MitchellStride/Clock-Module/images/20251205_routed.png

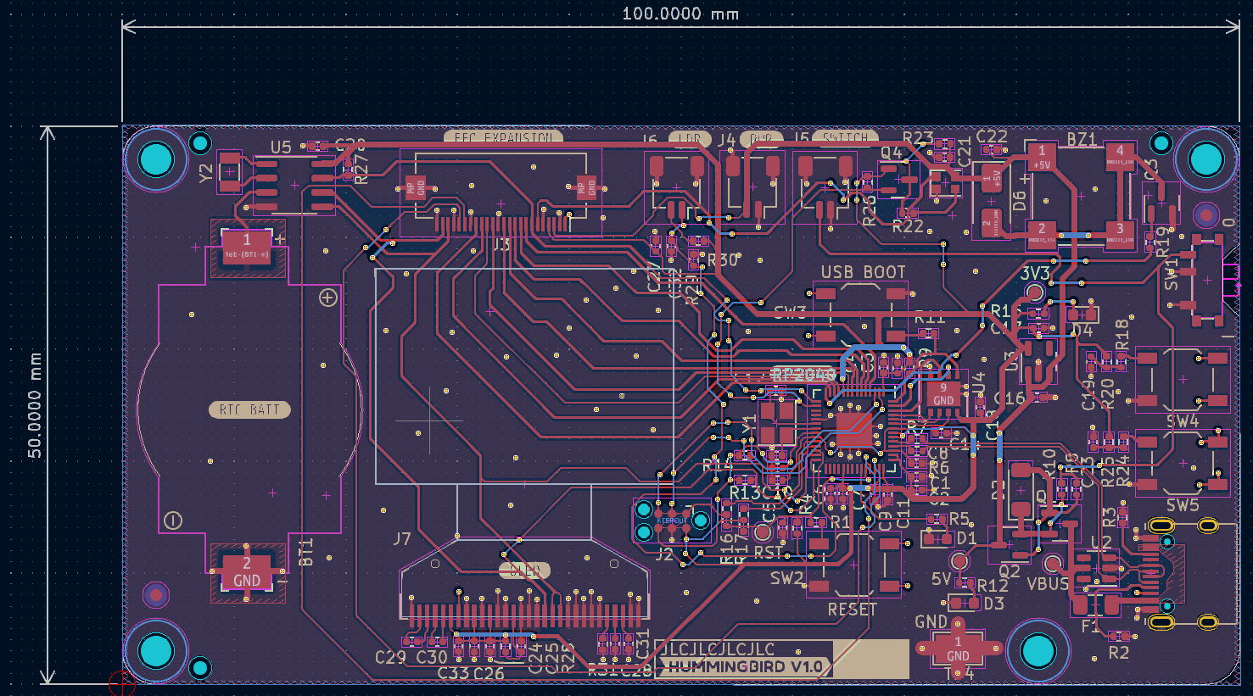
images/20251205_routed.png
