MitchellStride/Clock-Module/images/20251205_top3d.png

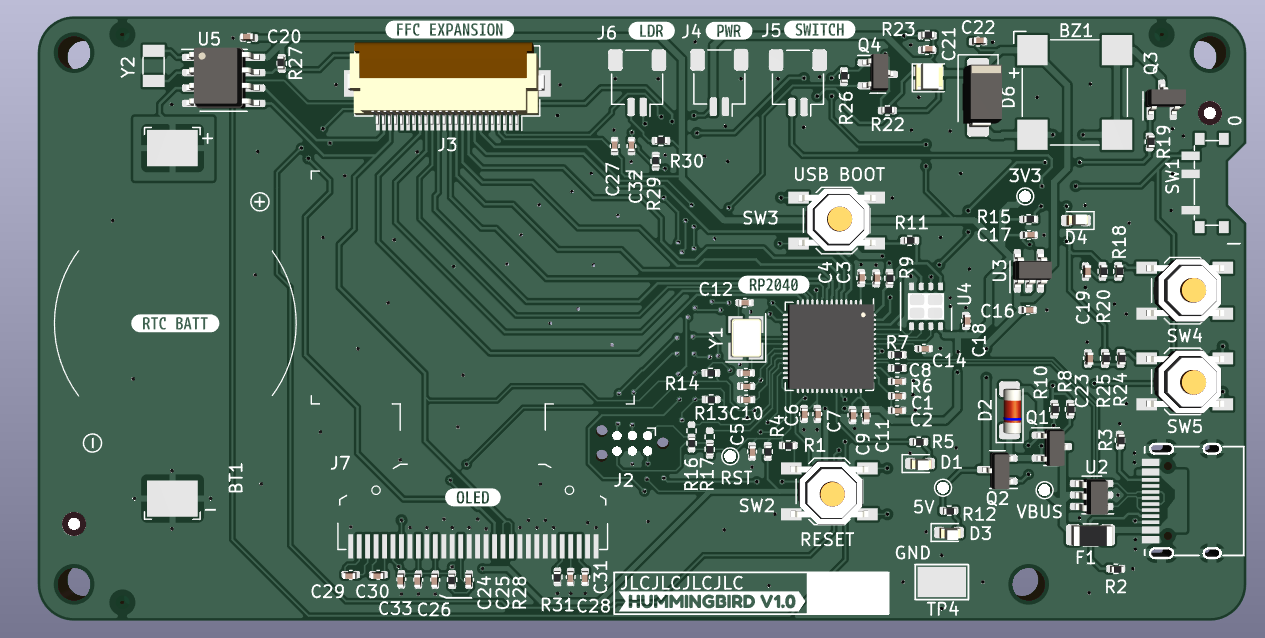
images/20251205_top3d.png
