MitchellStride/Clock-Module/images/assets/flower.PNG

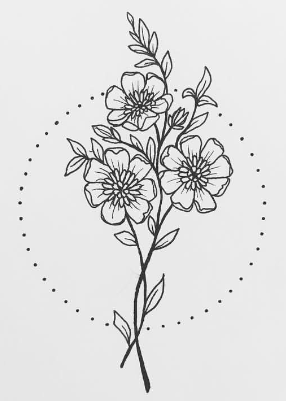
images/assets/flower.PNG
