MitchellStride/Clock-Module/images/assets/hummingbird.PNG

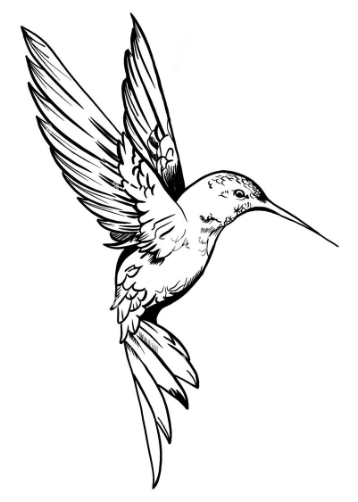
images/assets/hummingbird.PNG
