MitchellStride/Clock-Module/images/cost2.png

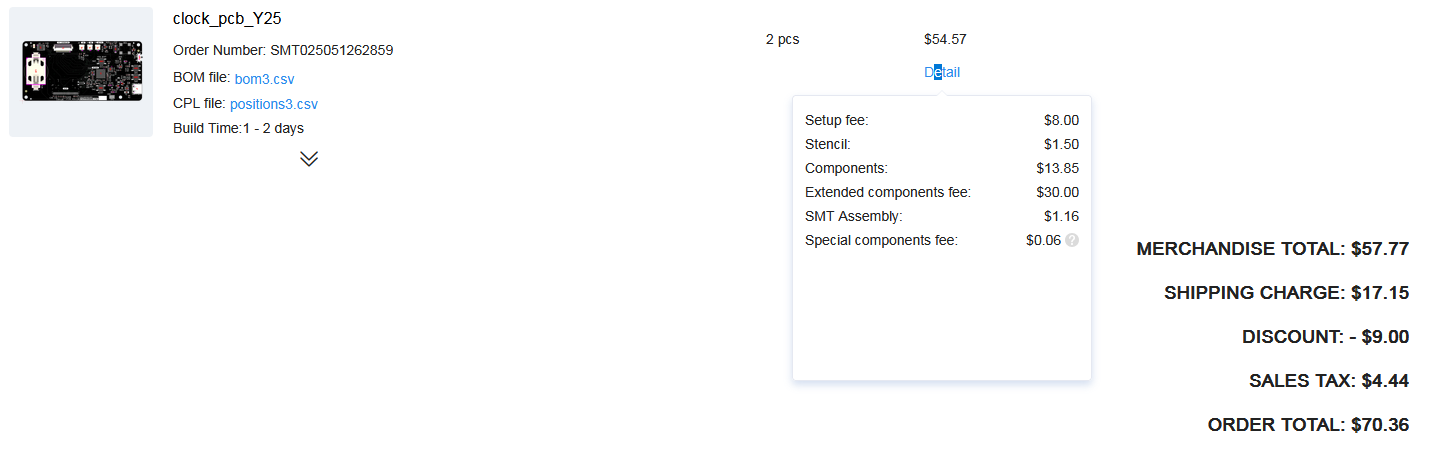
images/cost2.png
