MitchellStride/Clock-Module/images/cost.png

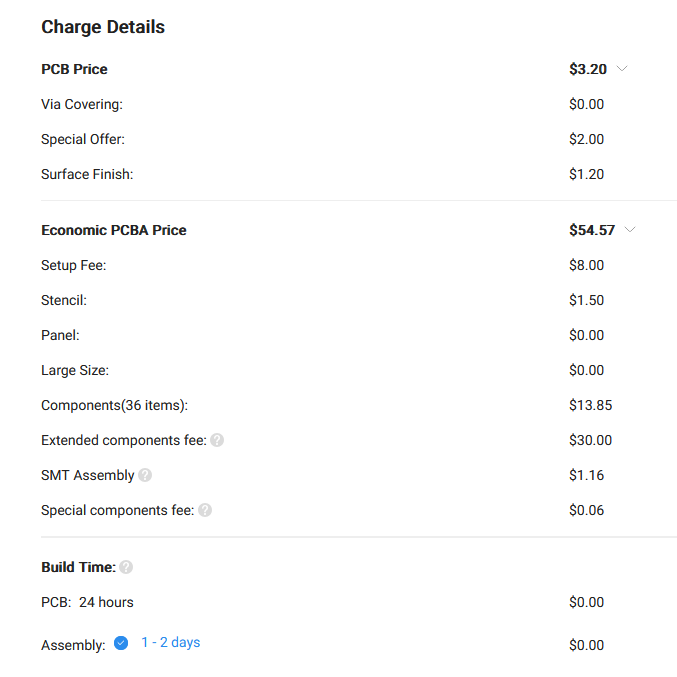
images/cost.png
