MitchellStride/Clock-Module/simulation/buzzer2.asc

C1: cap; 10µ
L1: ind; 3m
M1: nmos; ""
R3: res; 0
R5: res; 33
R6: res; 500
V1: voltage; 3.3
V2: voltage; 5
V3: voltage; PULSE(0 3.3 0.25m 0 0 0.25m 0.50m 10)
Named nets: 3V3, 0, 5V, 3v3_PULSE
.include C:\\Users\\stride\\Documents\\GitHub\\Clock-Module\\clock_pcb\\sim\\AO3401.mod
.tran 0.00375
.include C:\\Users\\stride\\Documents\\GitHub\\Clock-Module\\clock_pcb\\sim\\AO3400.mod
.model switch1 SW(Ron=0.2 Roff=10Meg Vt=.5 Vh=-.4)
