MitchellStride/Clock-Module/simulation/buzzer.asc

C1: cap; 10µ
M1: nmos; ""
R3: res; 120
R5: res; 10
R6: res; 10k
V1: voltage; 3.3
V2: voltage; 5
V3: voltage; PULSE(0 5 200m 0 0 200m 400m)
Named nets: 3V3, 0, 5V, 5V_PULSE
.include C:\\projects\\Death-Clock\\clock_pcb\\sim\\AO3401.mod
.tran 1
.include C:\\projects\\Death-Clock\\clock_pcb\\sim\\AO3400.mod
.model switch1 SW(Ron=0.2 Roff=10Meg Vt=.5 Vh=-.4)
