MitchellStride/Clock-Module/simulation/LDR.asc

C1: cap; 0.1µ
R1: res; 10k
R2: res; 10k
R3: res; 1k
V1: voltage; PULSE(0 3.3 0.1m 0.3m 0 1 2 1)
V2: voltage; 5
Named nets: 3V3, 0, 5V, ADC
.tran 50m
LDR
