MitchellStride/Clock-Module/simulation/lvl_shifter.asc

M1: nmos; ""
M2: nmos; 2N7002
R3: res; 10k
R4: res; 250K
R5: res; 10k
V1: voltage; 3.3
V2: voltage; 5
V3: voltage; PULSE(0 5 1.25m 0 0 1.25m 2.5m 100)
V4: voltage; PULSE(0 3.3 1.25m 0 0 1.25m 2.5m 100)
X1: jumper
Named nets: 3V3, 0, 5V, 5V_PULSE, LV_SIG, HV_SIG, 3V3_PULSE
.tran 20m
.model switch1 SW(Ron=0.2 Roff=10Meg Vt=.5 Vh=-.4)
.include C:\\projects\\Death-Clock\\clock_pcb\\sim\\AO3401.mod
.include C:\\projects\\Death-Clock\\clock_pcb\\sim\\AO3400.mod
