MitchellStride/Clock-Module/simulation/usb_pwr_sel.asc

D1: zener; PTZ6_2B
M1: pmos; ""
M2: pmos; ""
R1: res; 100k
R2: res; 100k
R4: res; 10
S1: sw; switch1
V1: voltage; 3.3
V2: voltage; 5
V3: voltage; PULSE(0 5 200m 0 0 200m 400m)
X2: jumper
Named nets: 3V3, 0, 5V, 5V_PULSE, VCC
.include C:\\Users\\mitch\\projects\\IOT-AutoHome\\esp8266_module\\sim\\AO3401.mod
.tran 1
.include C:\\Users\\mitch\\projects\\IOT-AutoHome\\esp8266_module\\sim\\AO3400.mod
RP
SW
.model switch1 SW(Ron=0.2 Roff=10Meg Vt=.5 Vh=-.4)
